juani13973/pedalinio-18-footswitches-prototype/Fusion 360 export files for production/Placa Pedales Drawing.jpg

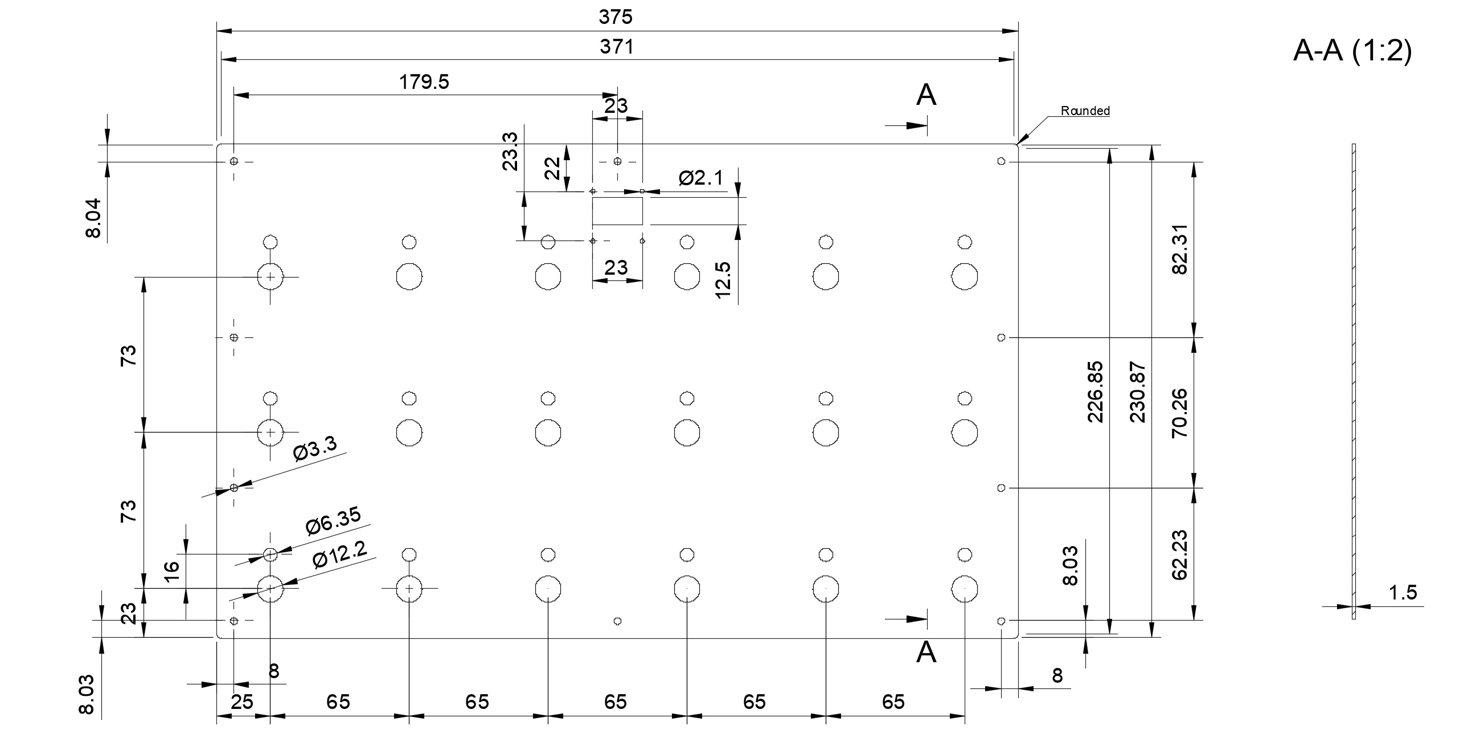
Fusion 360 export files for production/Placa Pedales Drawing.jpg
